danielmartinez/eClarin-legacy/vs10xx.h

/*
 * vs10xx.h
 * A library for MusicShield 2.0
 *
 * Copyright (c) 2012 seeed technology inc.
 * Website    : www.seeed.cc
 * Author     : Jack Shao (jacky.shaoxg@gmail.com)
 * Create Time: Mar 2014
 * Change Log :
 *
 * The MIT License (MIT)
 *
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
 * THE SOFTWARE IS PROVIDED "AS IS", WITHOUT WARRANTY OF ANY KIND, EXPRESS OR
 * IMPLIED, INCLUDING BUT NOT LIMITED TO THE WARRANTIES OF MERCHANTABILITY,
 * FITNESS FOR A PARTICULAR PURPOSE AND NONINFRINGEMENT. IN NO EVENT SHALL THE
 * AUTHORS OR COPYRIGHT HOLDERS BE LIABLE FOR ANY CLAIM, DAMAGES OR OTHER
 * LIABILITY, WHETHER IN AN ACTION OF CONTRACT, TORT OR OTHERWISE, ARISING FROM,
 * OUT OF OR IN CONNECTION WITH THE SOFTWARE OR THE USE OR OTHER DEALINGS IN
 * THE SOFTWARE.
 */


#ifndef VS10XX_H
#define VS10XX_H
#include <SPI.h>

/** VS10xx SCI Write Command byte is 0x02 */
#define VS_WRITE_COMMAND 0x02
/** VS10xx SCI Read Command byte is 0x03 */
#define VS_READ_COMMAND 0x03


#define SPI_MODE	0x0   /**< VS10xx register */
#define SPI_STATUS	0x1   /**< VS10xx register */
#define SPI_BASS	0x2   /**< VS10xx register */
#define SPI_CLOCKF	0x3   /**< VS10xx register */
#define SPI_DECODE_TIME	0x4   /**< VS10xx register */
#define SPI_AUDATA	0x5   /**< VS10xx register */
#define SPI_WRAM	0x6   /**< VS10xx register */
#define SPI_WRAMADDR	0x7   /**< VS10xx register */
#define SPI_HDAT0	0x8   /**< VS10xx register */
#define SPI_HDAT1	0x9   /**< VS10xx register */
#define SPI_AIADDR	0xa   /**< VS10xx register */
#define SPI_VOL		0xb   /**< VS10xx register */
#define SPI_AICTRL0	0xc   /**< VS10xx register */
#define SPI_AICTRL1	0xd   /**< VS10xx register */
#define SPI_AICTRL2	0xe   /**< VS10xx register */
#define SPI_AICTRL3	0xf   /**< VS10xx register */

#define SM_DIFF		0x01   /**< VS10xx register */
#define SM_JUMP		0x02   /**< VS10xx register */
#define SM_RESET	0x04   /**< VS10xx register */
#define SM_OUTOFWAV	0x08   /**< VS10xx register */
#define SM_PDOWN	0x10   /**< VS10xx register */
#define SM_TESTS	0x20   /**< VS10xx register */
#define SM_STREAM	0x40   /**< VS10xx register */
#define SM_PLUSV	0x80   /**< VS10xx register */
#define SM_DACT		0x100   /**< VS10xx register */
#define SM_SDIORD	0x200   /**< VS10xx register */
#define SM_SDISHARE	0x400   /**< VS10xx register */
#define SM_SDINEW	0x800   /**< VS10xx register */
#define SM_ADPCM        0x1000   /**< VS10xx register */
#define SM_ADPCM_HP     0x2000   /**< VS10xx register */
class VS10XX : public SPIClass
{
public:
  VS10XX(uint8_t _VS_XRESET, uint8_t _VS_DREQ, uint8_t _VS_XDCS, uint8_t _VS_XCS);
  void selectControlBus(void)   { digitalWrite(VS_XCS, LOW);}
  void deselectControlBus(void) { digitalWrite(VS_XCS, HIGH);}
  void selectDataBus(void)      { digitalWrite(VS_XDCS, LOW);}
  void deselectDataBus(void)    { digitalWrite(VS_XDCS, HIGH);}
  void putInReset(void)         { digitalWrite(VS_XRESET, LOW);}
  void releaseFromReset(void)   { digitalWrite(VS_XRESET, HIGH);}
  char readDREQ(void) { return digitalRead(VS_DREQ);}
  void init(void);
  void initForMidiFmt(void);
  void loadMidiPlugin(void);
  void initIO(void);
  void writeRegister(unsigned char addressbyte, unsigned char highbyte, unsigned char lowbyte);
  void writeRegister(unsigned char addressbyte, unsigned int value);
  void writeData(unsigned char *databuf, unsigned char = 32); //write 32 bytes to vs1053
  unsigned int readRegister(unsigned char addressbyte); /** Read the 16-bit value of a VS10xx register */
  void reset(void); //reset for vs10xx
  void softReset(void); /* Soft Reset of VS10xx (Between songs) */
  void setVolume(unsigned char leftchannel, unsigned char rightchannel); /* Set VS10xx Volume Register */
  void sendZerosToVS10xx(void); /** Send 2048 zeros. \todo Timeouts for all DREQ busy loop waits! */
private:
  uint8_t VS_XRESET;
  uint8_t VS_DREQ;
  uint8_t VS_XDCS;
  uint8_t VS_XCS;
};

/* For recording func */
#if defined(__AVR_ATmega1280__)|| defined(__AVR_ATmega2560__)

#ifndef SKIP_PLUGIN_VARNAME
#define PLUGIN_SIZE 13675
PROGMEM const unsigned short plugin[13675] = { /* Compressed plugin */
#endif
  0x0007, 0x0001, 0xc01a, 0x0006, 0x0001, 0x0002, 0x0007, 0x0001, /*    0 */
  0x1800, 0x0006, 0x8006, 0x0000, 0x0007, 0x0001, 0x8034, 0x0006, /*    8 */
  0x003a, 0x0000, 0x1350, 0xf400, 0x5404, 0x0000, 0x0811, 0xf400, /*   10 */
  0x5644, 0xf400, 0x5404, 0xf400, 0x5648, 0xf400, 0x5404, 0xf400, /*   18 */
  0x5654, 0xf400, 0x5404, 0xf400, 0x5640, 0x0000, 0x800a, 0x000c, /*   20 */
  0x0000, 0x0006, 0xc010, 0xb182, 0xa3c0, 0x0030, 0x0251, 0x3900, /*   28 */
  0x6000, 0x0030, 0x0691, 0x3900, 0x4024, 0x0000, 0x0090, 0x0000, /*   30 */
  0x4000, 0x3810, 0x0024, 0x0000, 0x4200, 0x3800, 0x0024, 0x2900, /*   38 */
  0x4c40, 0x0006, 0x2016, 0x2a00, 0x040e, 0x2a00, 0x144e, 0x2a00, /*   40 */
  0x218e, 0x2a00, 0x314e, 0x0007, 0x0001, 0x8010, 0x0006, 0x001e, /*   48 */
  0x3009, 0x3851, 0x3e14, 0xf812, 0x3e11, 0xb817, 0x0000, 0x00d7, /*   50 */
  0x0020, 0x03d2, 0x3704, 0xc024, 0x0030, 0x0551, 0x3009, 0x0e06, /*   58 */
  0x3911, 0x8e06, 0x3961, 0x9bcc, 0x3f04, 0xc024, 0x36f1, 0x9817, /*   60 */
  0x36f4, 0xd812, 0x2100, 0x0000, 0x3904, 0x5bd1, 0x0007, 0x0001, /*   68 */
  0x8051, 0x0006, 0x006a, 0x3e02, 0xb857, 0x3e02, 0x7848, 0x3e08, /*   70 */
  0x3861, 0x3e08, 0xb863, 0x3e00, 0x7840, 0x0030, 0x0417, 0x3700, /*   78 */
  0x0024, 0x0000, 0x0201, 0x6012, 0x0024, 0x0006, 0xc017, 0x2800, /*   80 */
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
  0xc670, 0x0015, 0xba54, 0x0015, 0xaef5, 0x0015, 0xa448, 0x0015, /* 3128 */
  0x9a42, 0x0015, 0x90d8, 0x0015, 0x8802, 0x0015, 0xff6a, 0x0016, /* 3130 */
  0xefd4, 0x0016, 0xe132, 0x0016, 0xd374, 0x0016, 0xc68d, 0x0016, /* 3138 */
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
#ifndef SKIP_PLUGIN_VARNAME
};
#endif
#endif




#endif
