danielmartinez/eClarin-legacy/GM1.h

const char instrument0[] PROGMEM = "Acoustic Grand Piano";
const char instrument1[] PROGMEM = "Bright Acoustic Piano";
const char instrument2[] PROGMEM = "Electric Grand Piano";
const char instrument3[] PROGMEM = "Honky-tonk Piano";
const char instrument4[] PROGMEM = "Electric Piano 1";
const char instrument5[] PROGMEM = "Electric Piano 2";
const char instrument6[] PROGMEM = "Harpsichord";
const char instrument7[] PROGMEM = "Clavinet";
const char instrument8[] PROGMEM = "Celesta";
const char instrument9[] PROGMEM = "Glockenspiel";
const char instrument10[] PROGMEM = "Music Box";
const char instrument11[] PROGMEM = "Vibraphone";
const char instrument12[] PROGMEM = "Marimba";
const char instrument13[] PROGMEM = "Xylophone";
const char instrument14[] PROGMEM = "Tubular Bells";
const char instrument15[] PROGMEM = "Dulcimer";
const char instrument16[] PROGMEM = "Drawbar Organ";
const char instrument17[] PROGMEM = "Percussive Organ";
const char instrument18[] PROGMEM = "Rock Organ";
const char instrument19[] PROGMEM = "Church Organ";
const char instrument20[] PROGMEM = "Reed Organ";
const char instrument21[] PROGMEM = "Accordion";
const char instrument22[] PROGMEM = "Harmonica";
const char instrument23[] PROGMEM = "Tango Accordion";
const char instrument24[] PROGMEM = "Acoustic Guitar (nylon)";
const char instrument25[] PROGMEM = "Acoustic Guitar (steel)";
const char instrument26[] PROGMEM = "Electric Guitar (jazz)";
const char instrument27[] PROGMEM = "Electric Guitar (clean)";
const char instrument28[] PROGMEM = "Electric Guitar (muted)";
const char instrument29[] PROGMEM = "Overdriven Guitar";
const char instrument30[] PROGMEM = "Distortion Guitar";
const char instrument31[] PROGMEM = "Guitar harmonics";
const char instrument32[] PROGMEM = "Acoustic Bass";
const char instrument33[] PROGMEM = "Electric Bass (finger)";
const char instrument34[] PROGMEM = "Electric Bass (pick)";
const char instrument35[] PROGMEM = "Fretless Bass";
const char instrument36[] PROGMEM = "Slap Bass 1";
const char instrument37[] PROGMEM = "Slap Bass 2";
const char instrument38[] PROGMEM = "Synth Bass 1";
const char instrument39[] PROGMEM = "Synth Bass 2";
const char instrument40[] PROGMEM = "Violin";
const char instrument41[] PROGMEM = "Viola";
const char instrument42[] PROGMEM = "Cello";
const char instrument43[] PROGMEM = "Contrabass";
const char instrument44[] PROGMEM = "Tremolo Strings";
const char instrument45[] PROGMEM = "Pizzicato Strings";
const char instrument46[] PROGMEM = "Orchestral Harp";
const char instrument47[] PROGMEM = "Timpani";
const char instrument48[] PROGMEM = "String Ensemble 1";
const char instrument49[] PROGMEM = "String Ensemble 2";
const char instrument50[] PROGMEM = "Synth Strings 1";
const char instrument51[] PROGMEM = "Synth Strings 2";
const char instrument52[] PROGMEM = "Choir Aahs";
const char instrument53[] PROGMEM = "Voice Oohs";
const char instrument54[] PROGMEM = "Synth Voice";
const char instrument55[] PROGMEM = "Orchestra Hit";
const char instrument56[] PROGMEM = "Trumpet";
const char instrument57[] PROGMEM = "Trombone";
const char instrument58[] PROGMEM = "Tuba";
const char instrument59[] PROGMEM = "Muted Trumpet";
const char instrument60[] PROGMEM = "French Horn";
const char instrument61[] PROGMEM = "Brass Section";
const char instrument62[] PROGMEM = "Synth Brass 1";
const char instrument63[] PROGMEM = "Synth Brass 2";
const char instrument64[] PROGMEM = "Soprano Sax";
const char instrument65[] PROGMEM = "Alto Sax";
const char instrument66[] PROGMEM = "Tenor Sax";
const char instrument67[] PROGMEM = "Baritone Sax";
const char instrument68[] PROGMEM = "Oboe";
const char instrument69[] PROGMEM = "English Horn";
const char instrument70[] PROGMEM = "Bassoon";
const char instrument71[] PROGMEM = "Clarinet";
const char instrument72[] PROGMEM = "Piccolo";
const char instrument73[] PROGMEM = "Flute";
const char instrument74[] PROGMEM = "Recorder";
const char instrument75[] PROGMEM = "Pan Flute";
const char instrument76[] PROGMEM = "Blown Bottle";
const char instrument77[] PROGMEM = "Shakuhachi";
const char instrument78[] PROGMEM = "Whistle";
const char instrument79[] PROGMEM = "Ocarina";
const char instrument80[] PROGMEM = "Lead 1 (square)";
const char instrument81[] PROGMEM = "Lead 2 (sawtooth)";
const char instrument82[] PROGMEM = "Lead 3 (calliope)";
const char instrument83[] PROGMEM = "Lead 4 (chiff)";
const char instrument84[] PROGMEM = "Lead 5 (charang)";
const char instrument85[] PROGMEM = "Lead 6 (voice)";
const char instrument86[] PROGMEM = "Lead 7 (fifths)";
const char instrument87[] PROGMEM = "Lead 8 (bass + lead)";
const char instrument88[] PROGMEM = "Pad 1 (new age)";
const char instrument89[] PROGMEM = "Pad 2 (warm)";
const char instrument90[] PROGMEM = "Pad 3 (polysynth)";
const char instrument91[] PROGMEM = "Pad 4 (choir)";
const char instrument92[] PROGMEM = "Pad 5 (bowed)";
const char instrument93[] PROGMEM = "Pad 6 (metallic)";
const char instrument94[] PROGMEM = "Pad 7 (halo)";
const char instrument95[] PROGMEM = "Pad 8 (sweep)";
const char instrument96[] PROGMEM = "FX 1 (rain)";
const char instrument97[] PROGMEM = "FX 2 (soundtrack)";
const char instrument98[] PROGMEM = "FX 3 (crystal)";
const char instrument99[] PROGMEM = "FX 4 (atmosphere)";
const char instrument100[] PROGMEM = "FX 5 (brightness)";
const char instrument101[] PROGMEM = "FX 6 (goblins)";
const char instrument102[] PROGMEM = "FX 7 (echoes)";
const char instrument103[] PROGMEM = "FX 8 (sci-fi)";
const char instrument104[] PROGMEM = "Sitar";
const char instrument105[] PROGMEM = "Banjo";
const char instrument106[] PROGMEM = "Shamisen";
const char instrument107[] PROGMEM = "Koto";
const char instrument108[] PROGMEM = "Kalimba";
const char instrument109[] PROGMEM = "Bag pipe";
const char instrument110[] PROGMEM = "Fiddle";
const char instrument111[] PROGMEM = "Shanai";
const char instrument112[] PROGMEM = "Tinkle Bell";
const char instrument113[] PROGMEM = "Agogo";
const char instrument114[] PROGMEM = "Steel Drums";
const char instrument115[] PROGMEM = "Woodblock";
const char instrument116[] PROGMEM = "Taiko Drum";
const char instrument117[] PROGMEM = "Melodic Tom";
const char instrument118[] PROGMEM = "Synth Drum";
const char instrument119[] PROGMEM = "Reverse Cymbal";
const char instrument120[] PROGMEM = "Guitar Fret Noise";
const char instrument121[] PROGMEM = "Breath Noise";
const char instrument122[] PROGMEM = "Seashore";
const char instrument123[] PROGMEM = "Bird Tweet";
const char instrument124[] PROGMEM = "Telephone Ring";
const char instrument125[] PROGMEM = "Helicopter";
const char instrument126[] PROGMEM = "Applause";
const char instrument127[] PROGMEM = "Gunshot";

const char* const instrumentNames[] PROGMEM = {
instrument0, instrument1, instrument2, instrument3, instrument4,
instrument5, instrument6, instrument7, instrument8, instrument9,
instrument10, instrument11, instrument12, instrument13,
instrument14, instrument15, instrument16, instrument17,
instrument18, instrument19, instrument20, instrument21,
instrument22, instrument23, instrument24, instrument25,
instrument26, instrument27, instrument28, instrument29,
instrument30, instrument31, instrument32, instrument33,
instrument34, instrument35, instrument36, instrument37,
instrument38, instrument39, instrument40, instrument41,
instrument42, instrument43, instrument44, instrument45,
instrument46, instrument47, instrument48, instrument49,
instrument50, instrument51, instrument52, instrument53,
instrument54, instrument55, instrument56, instrument57,
instrument58, instrument59, instrument60, instrument61,
instrument62, instrument63, instrument64, instrument65,
instrument66, instrument67, instrument68, instrument69,
instrument70, instrument71, instrument72, instrument73,
instrument74, instrument75, instrument76, instrument77,
instrument78, instrument79, instrument80, instrument81,
instrument82, instrument83, instrument84, instrument85,
instrument86, instrument87, instrument88, instrument89,
instrument90, instrument91, instrument92, instrument93,
instrument94, instrument95, instrument96, instrument97,
instrument98, instrument99, instrument100, instrument101,
instrument102, instrument103, instrument104, instrument105,
instrument106, instrument107, instrument108, instrument109,
instrument110, instrument111, instrument112, instrument113,
instrument114, instrument115, instrument116, instrument117,
instrument118, instrument119, instrument120, instrument121,
instrument122, instrument123, instrument124, instrument125,
instrument126, instrument127};
